mdl29/emoji-shooter/frontend/asset/targets/christian.webp

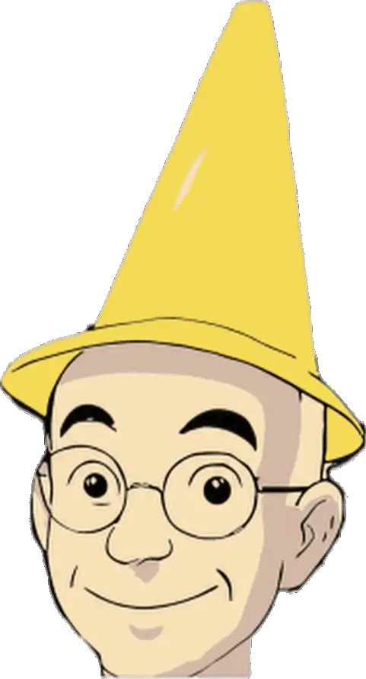
frontend/asset/targets/christian.webp
