mdl29/emoji-shooter/frontend/asset/targets/thibault.webp

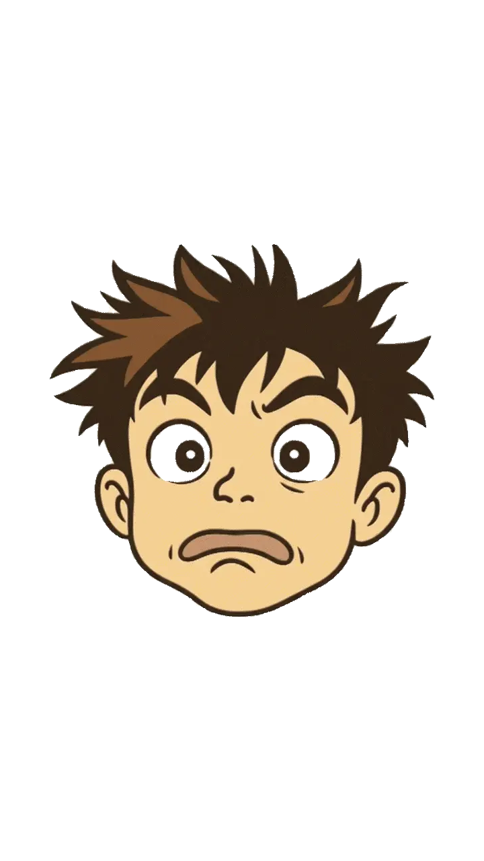
frontend/asset/targets/thibault.webp
